stevexyz/microtron/datasheets/74ls273 - 8bit FF with Reset.png

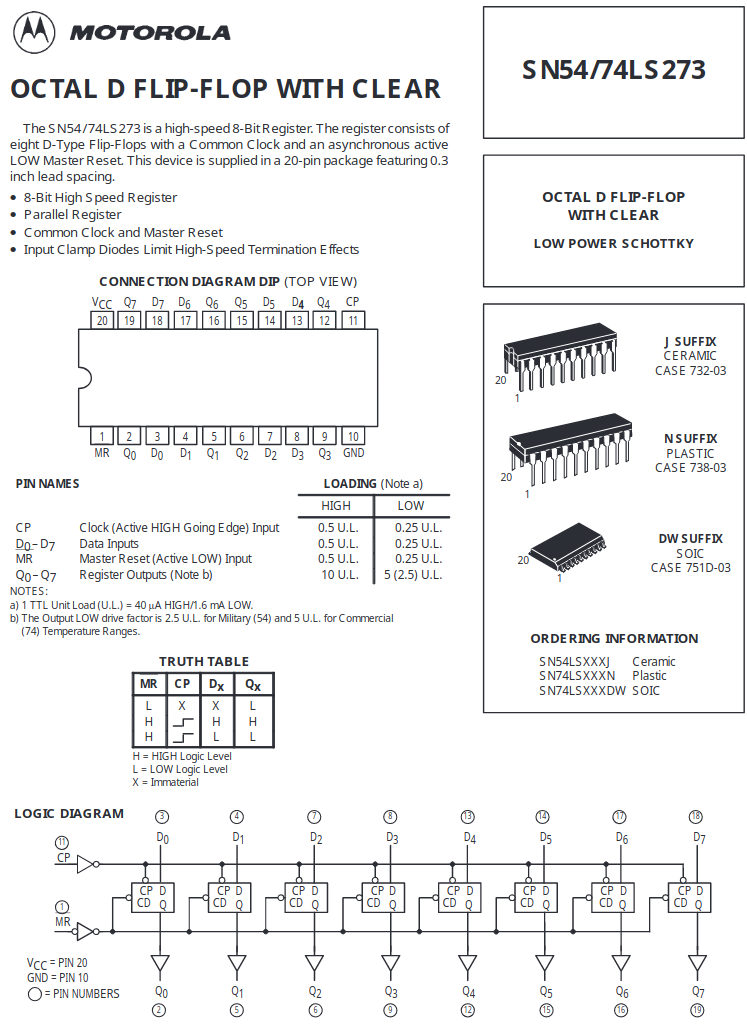
datasheets/74ls273 - 8bit FF with Reset.png
