stevexyz/microtron/datasheets/74ls373ls374 -- latch FF with 3state a.png

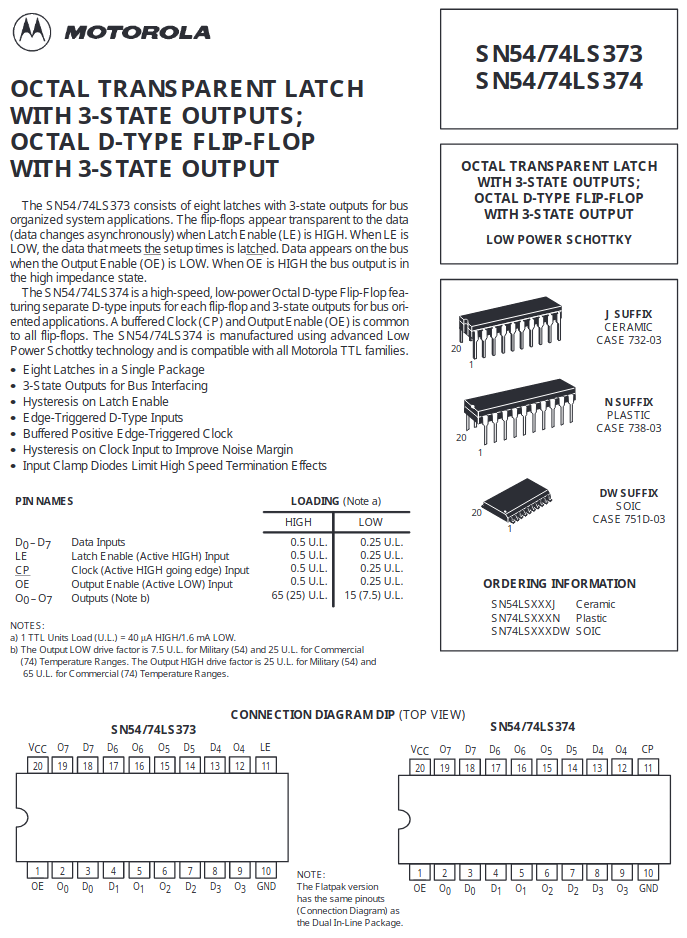
datasheets/74ls373ls374 -- latch FF with 3state a.png
