stevexyz/microtron/datasheets/74ls373ls374 -- latch FF with 3state b.png

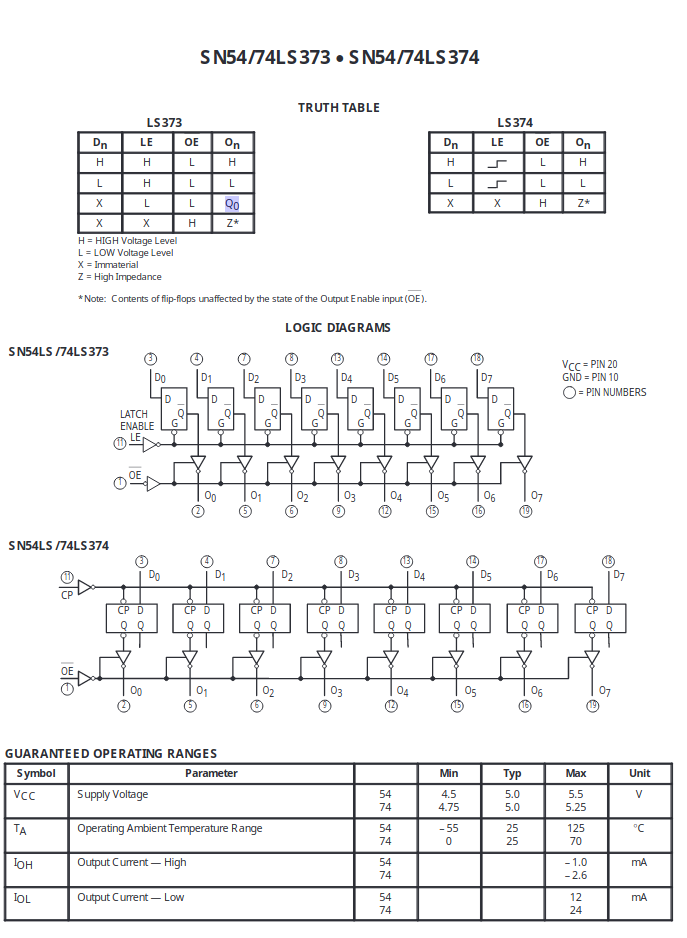
datasheets/74ls373ls374 -- latch FF with 3state b.png
