stevexyz/microtron/datasheets/74ls377 8bit FF c.png

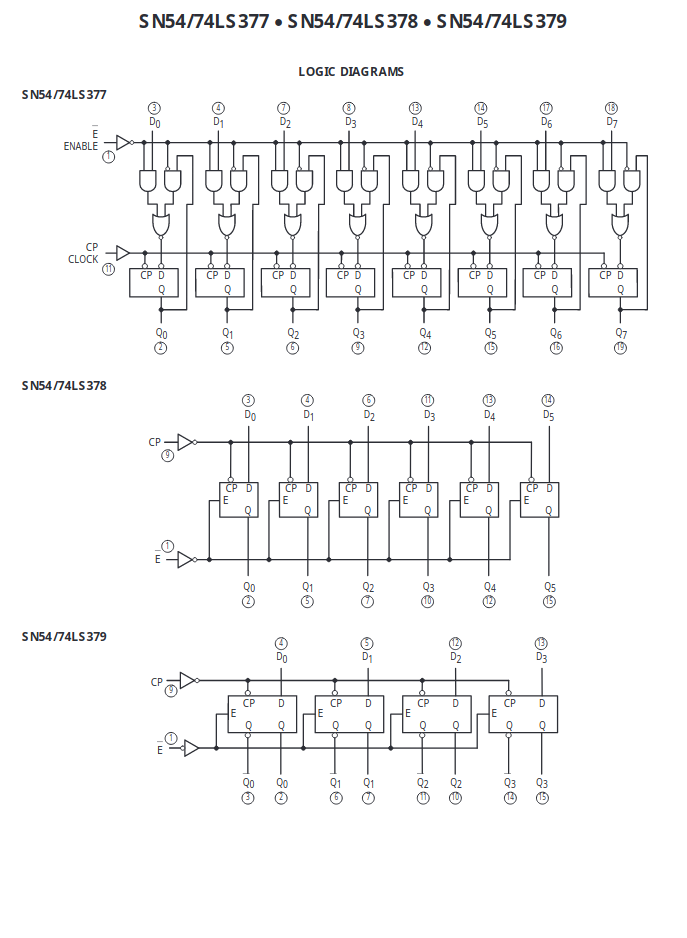
datasheets/74ls377 8bit FF c.png
