stevexyz/microtron/datasheets/74ls377 8bit FF d.png

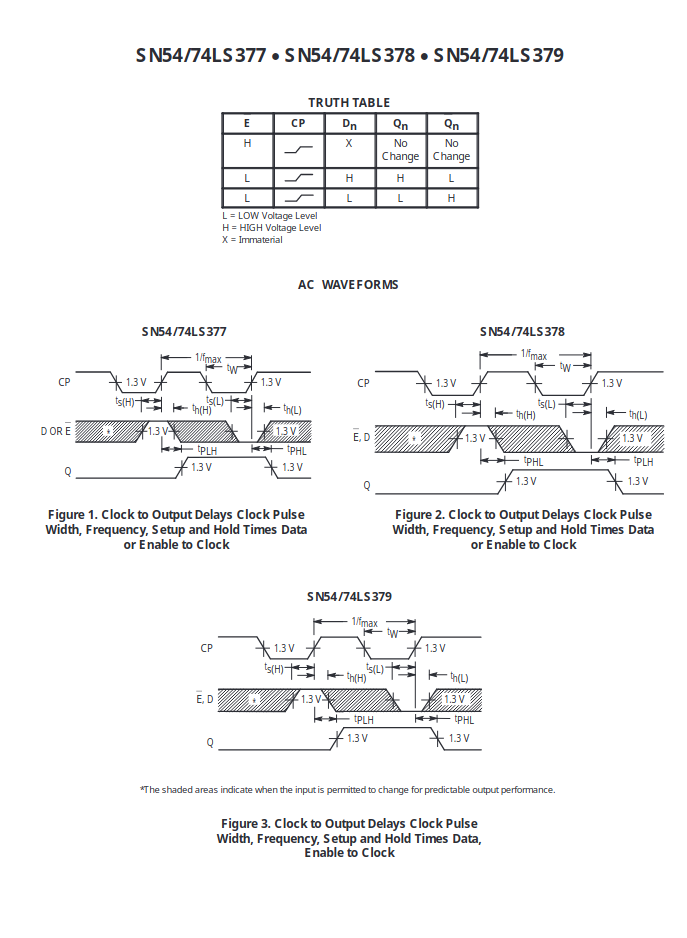
datasheets/74ls377 8bit FF d.png
