stevexyz/microtron/datasheets/7404.png

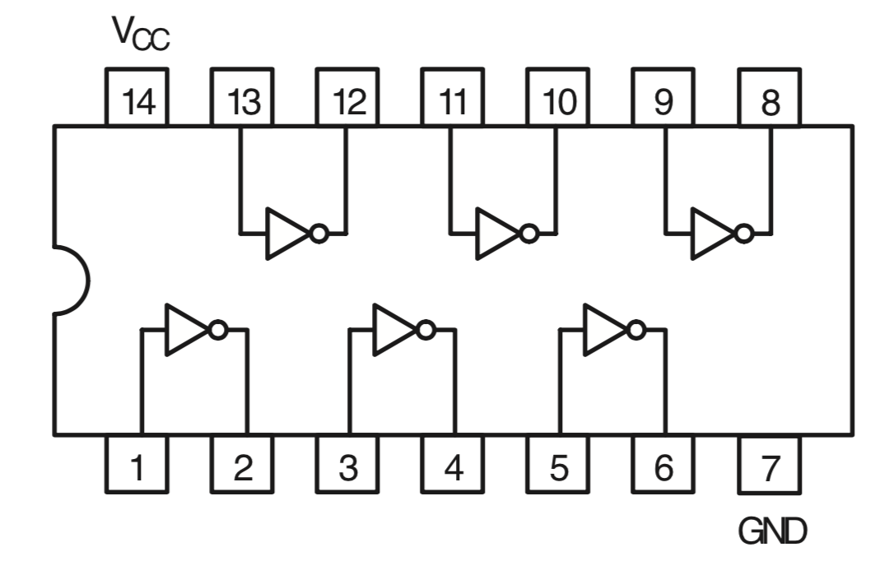
datasheets/7404.png
