stevexyz/microtron/datasheets/7432.png

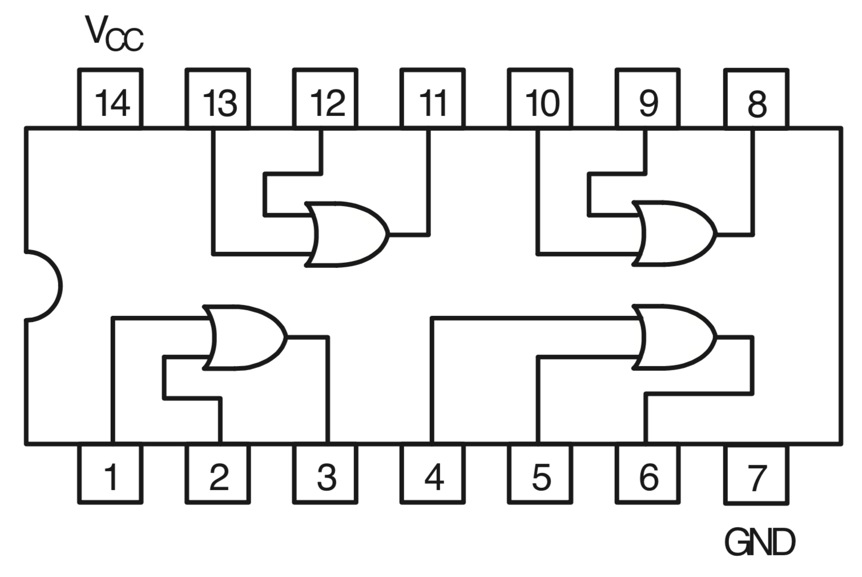
datasheets/7432.png
