stevexyz/microtron/datasheets/62256.png

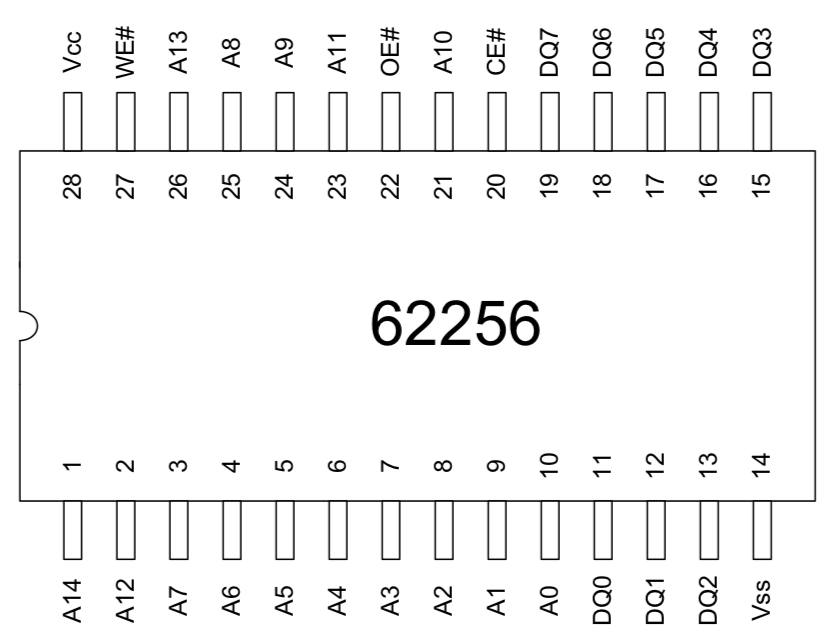
datasheets/62256.png
