stevexyz/microtron/datasheets/74138.png

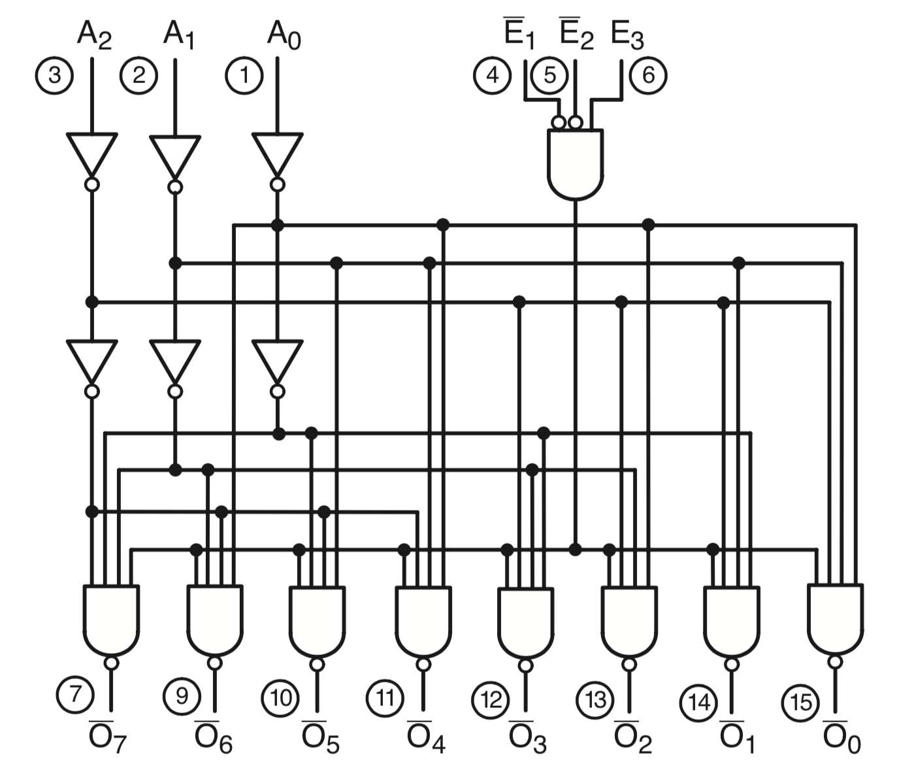
datasheets/74138.png
