stevexyz/microtron/datasheets/74139.png

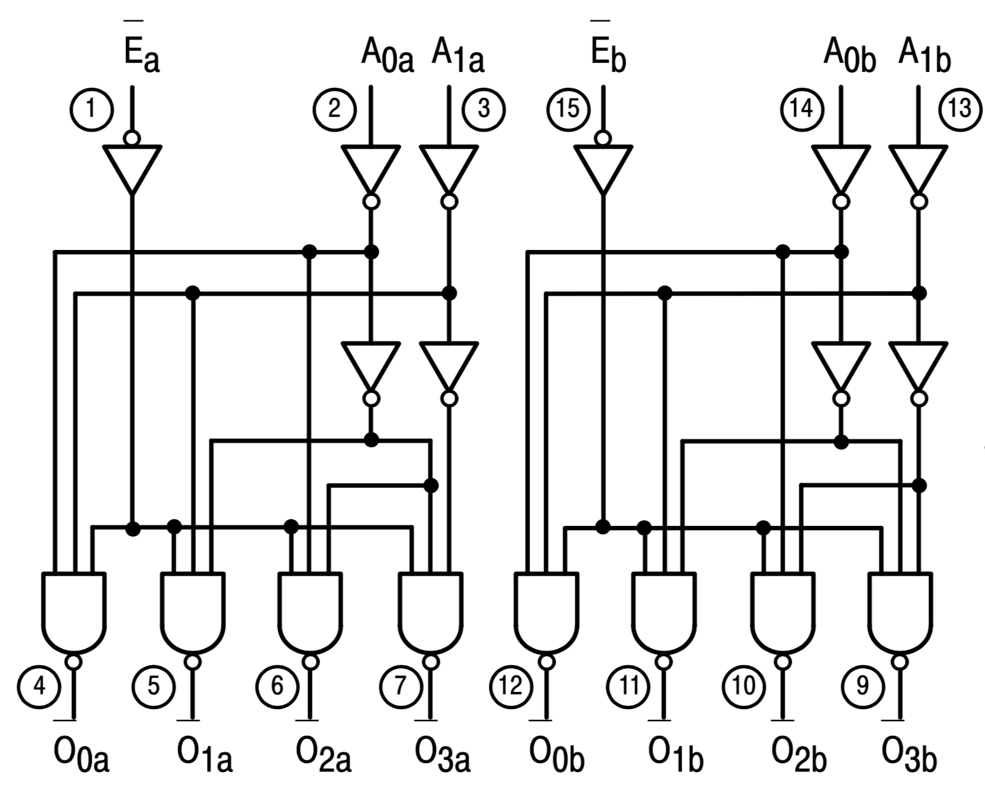
datasheets/74139.png
