stevexyz/microtron/datasheets/74153.png

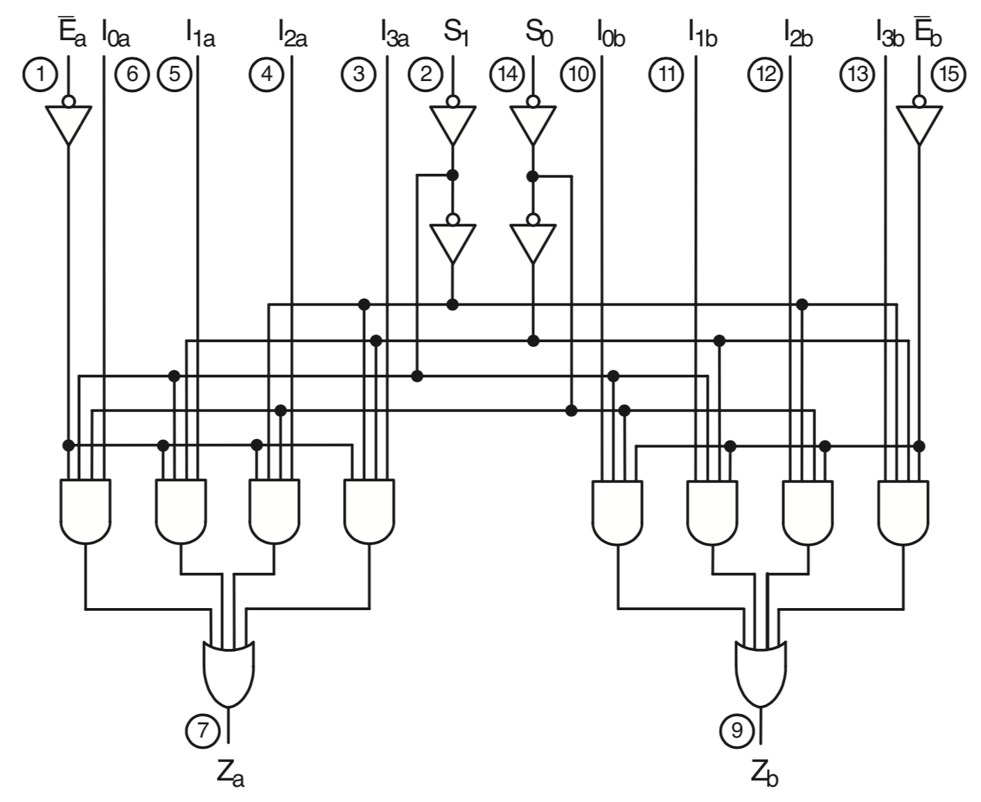
datasheets/74153.png
