stevexyz/microtron/datasheets/74157.png

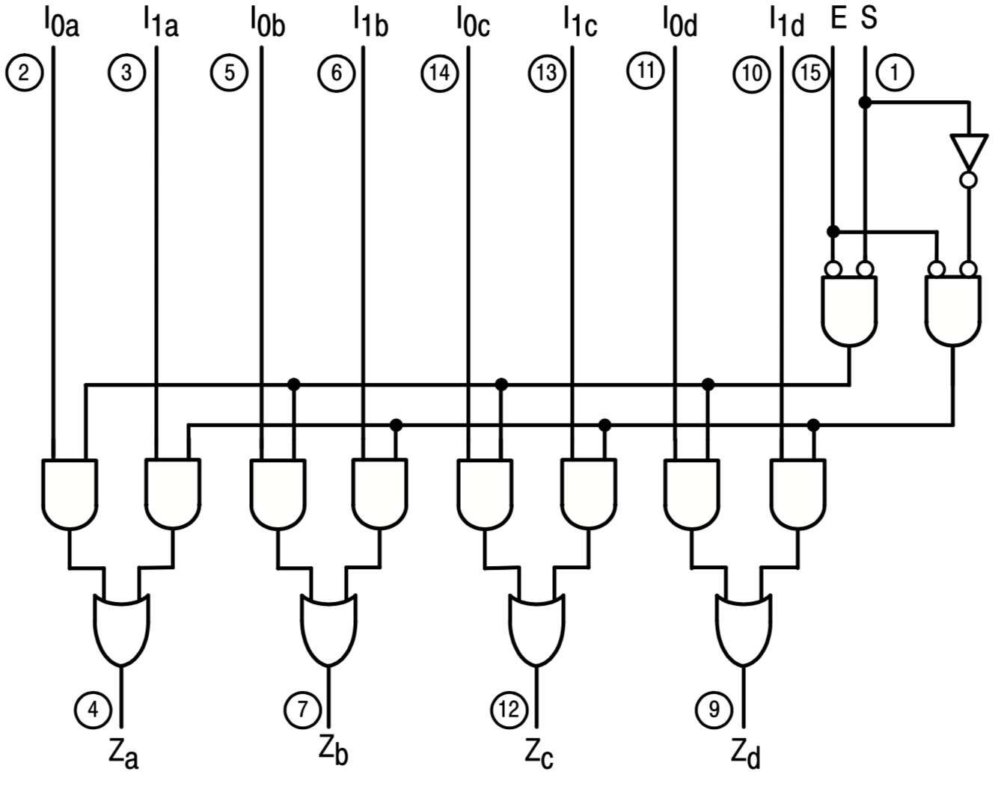
datasheets/74157.png
