stevexyz/microtron/datasheets/74161.png

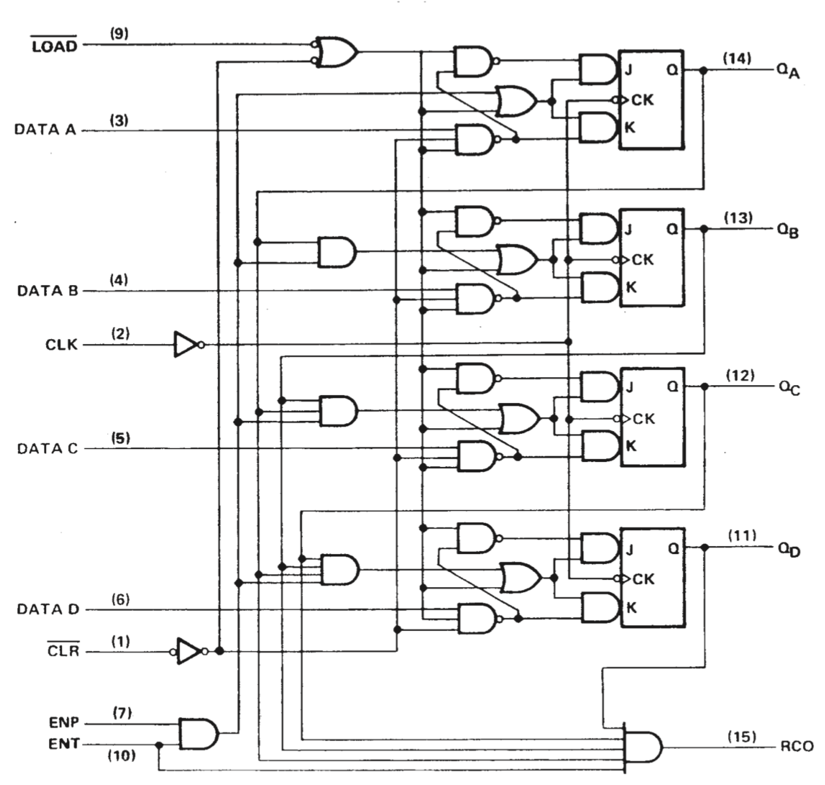
datasheets/74161.png
