stevexyz/microtron/datasheets/74240.png

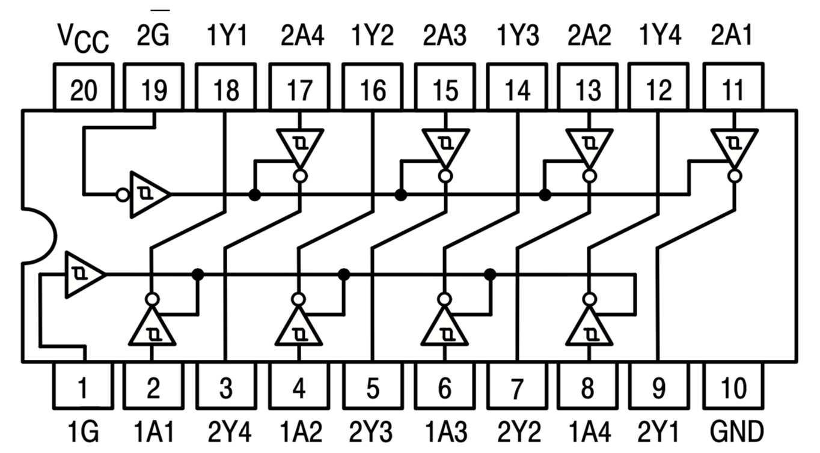
datasheets/74240.png
