stevexyz/microtron/datasheets/74244.png

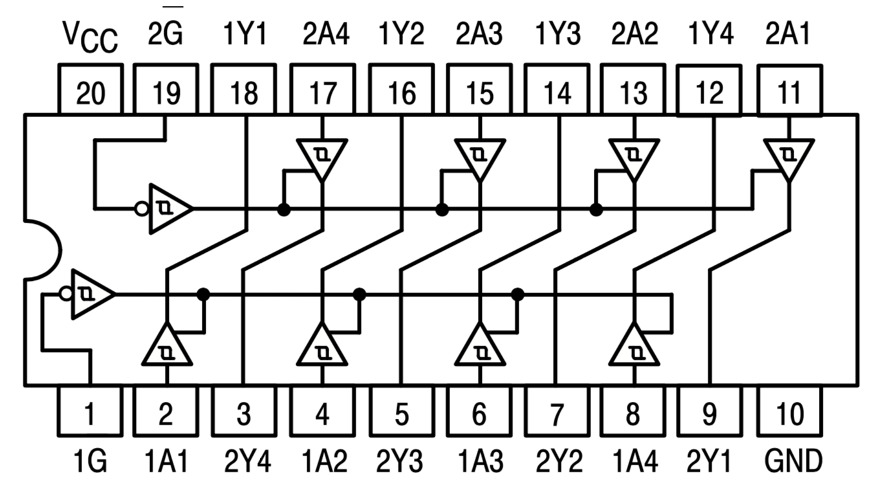
datasheets/74244.png
