stevexyz/microtron/datasheets/74273.png

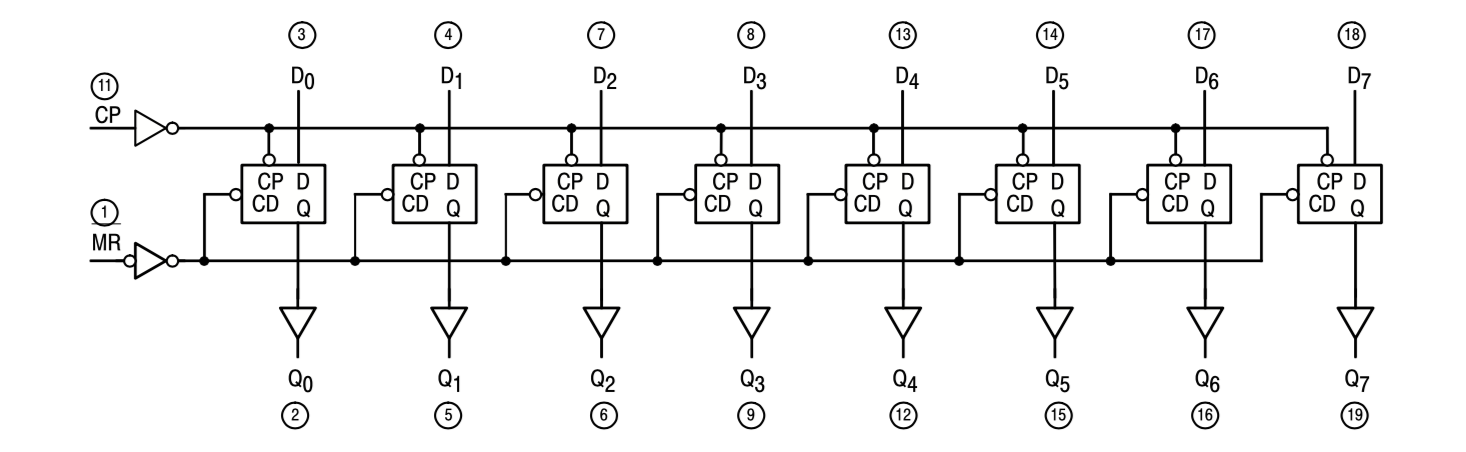
datasheets/74273.png
