stevexyz/microtron/datasheets/74283.png

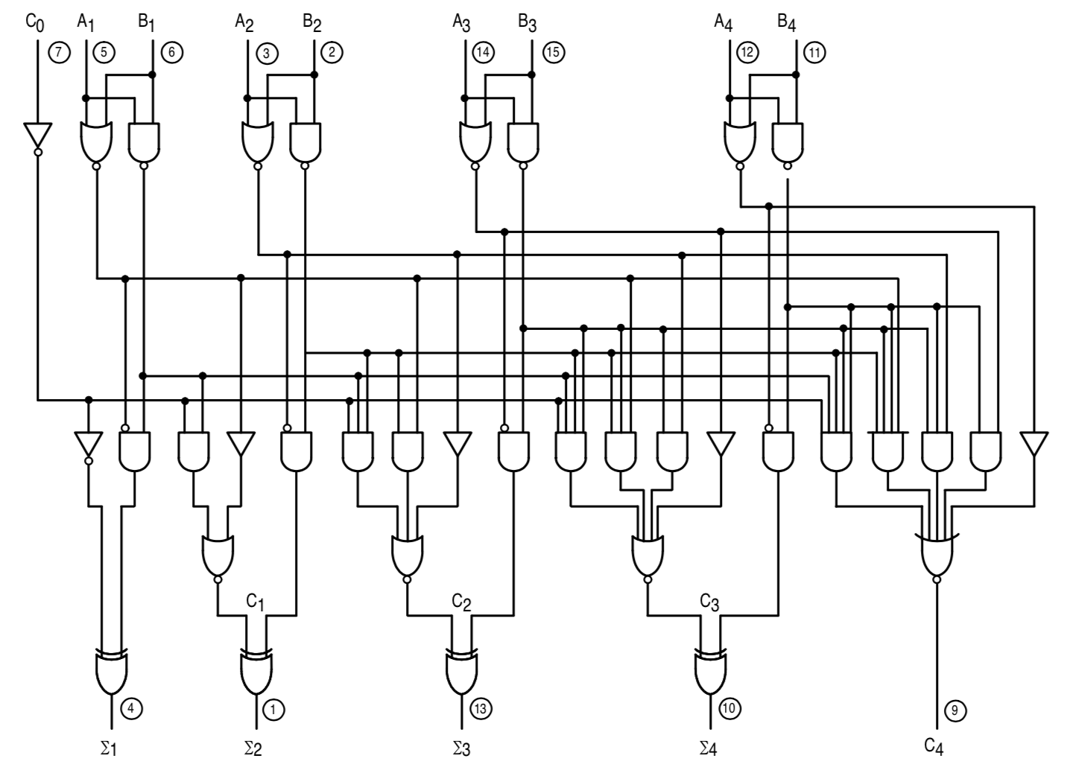
datasheets/74283.png
