stevexyz/microtron/datasheets/74377.png

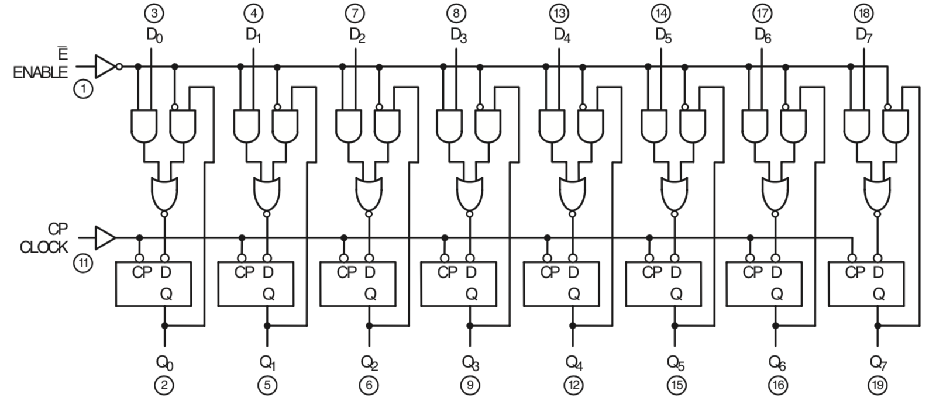
datasheets/74377.png
