stevexyz/microtron/datasheets/74595.png

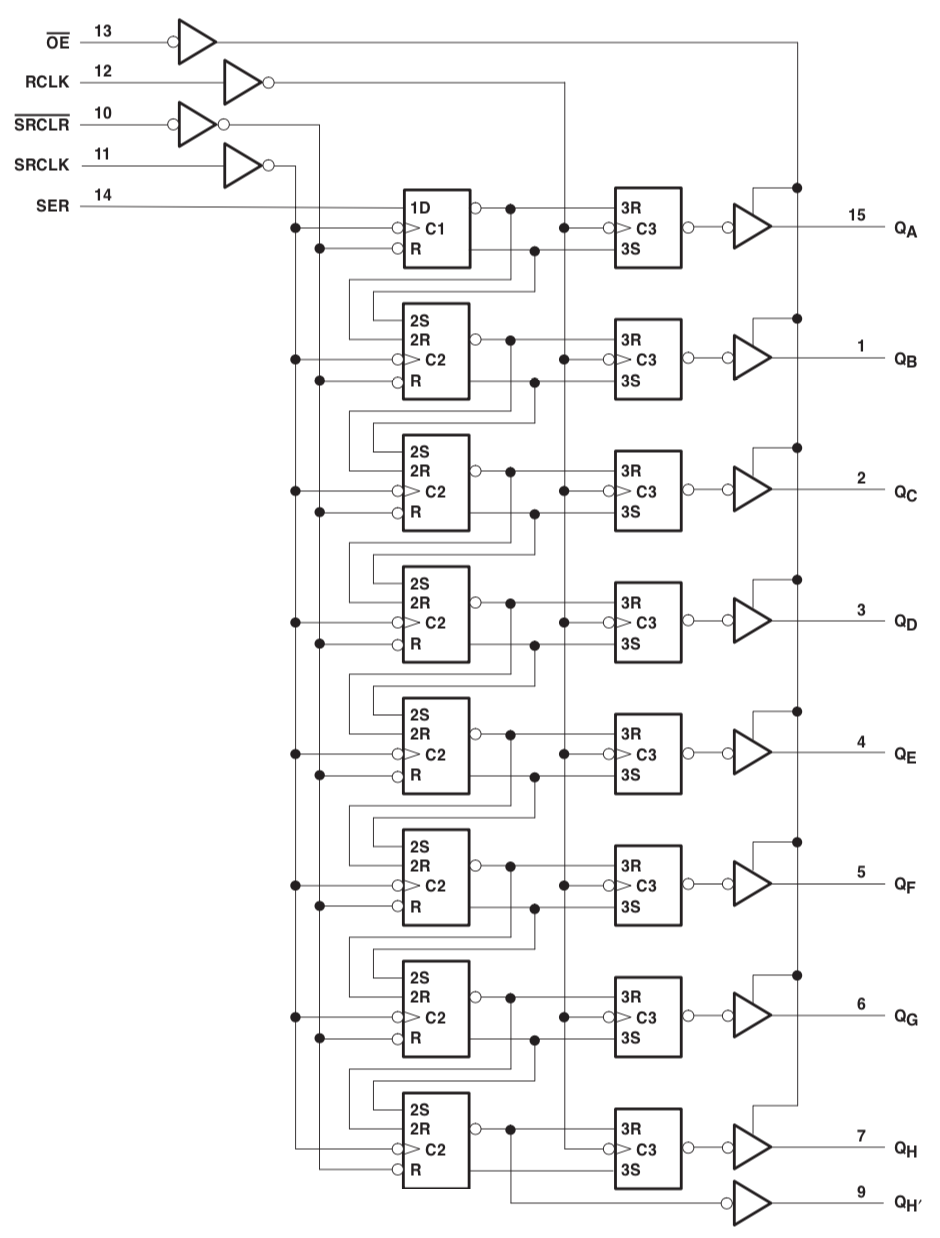
datasheets/74595.png
