stevexyz/microtron/datasheets/MCP100.png

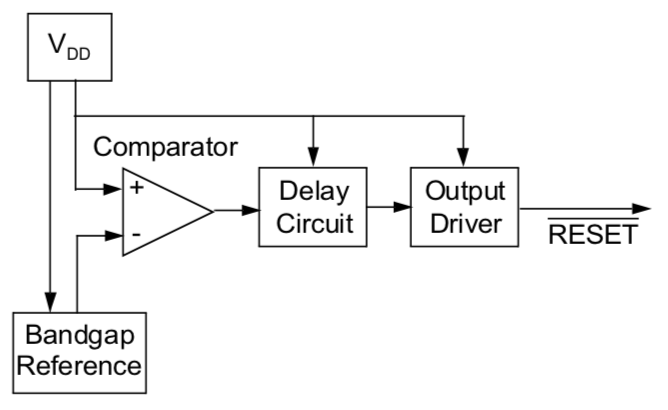
datasheets/MCP100.png
